frankvg/Pet-Detective/sketch_pet_detective/GIF_cats.h

/*  Pet Detective, by FAQware

These are small GIF images converted into bytes
You will need to change source code and layouts if you elect to change the image sizes
We use this GIF to filearray converter: https://mischianti.org/online-converter-file-to-cpp-gzip-byte-array-3/

Transpanacy MUST be turned off when creating your GIF.  Background should be black.
*/

//File: Cat_Detective_Jacket_141x140.gif, Size: 14034
#define Cat_Detective_Jacket_141x140_gif_len 14034
const uint8_t Cat_Detective_Jacket_141x140_gif[] PROGMEM = {  
0x47, 0x49, 0x46, 0x38, 0x39, 0x61, 0x8D, 0x00, 0x8C, 0x00, 0xF7, 0x00, 0x00, 0xC8, 0xB9, 0xA4, 
0xA9, 0x93, 0x78, 0x88, 0x6B, 0x53, 0xB3, 0x8C, 0x67, 0xC9, 0xB4, 0x99, 0x9A, 0x83, 0x68, 0xB9, 
0xA4, 0x8A, 0x49, 0x2E, 0x18, 0xC3, 0x9C, 0x7B, 0xCA, 0xA4, 0x84, 0xA3, 0x7B, 0x57, 0x93, 0x69, 
0x33, 0x53, 0x3B, 0x28, 0xD6, 0xC2, 0xAA, 0x8C, 0x72, 0x57, 0x26, 0x19, 0x11, 0xB9, 0xA9, 0x95, 
0x59, 0x46, 0x34, 0x97, 0x7C, 0x62, 0x93, 0x6C, 0x4B, 0x8F, 0x5A, 0x2C, 0x6B, 0x51, 0x39, 0xD4, 
0xB2, 0x93, 0xD2, 0xAC, 0x8D, 0xE6, 0xD3, 0xBA, 0x93, 0x72, 0x53, 0x39, 0x2C, 0x22, 0xAA, 0x99, 
0x84, 0xF5, 0xE9, 0xD8, 0xC7, 0xA4, 0x79, 0x9C, 0x7A, 0x5C, 0xE6, 0xC8, 0xA5, 0x7C, 0x61, 0x48, 
0xA8, 0x81, 0x5A, 0xAD, 0x71, 0x34, 0x9A, 0x89, 0x73, 0xB9, 0x92, 0x6A, 0xCE, 0xAA, 0x8B, 0x68, 
0x55, 0x44, 0xD5, 0xB5, 0x8B, 0xEB, 0xDD, 0xCB, 0xC7, 0xA1, 0x82, 0x8D, 0x69, 0x4A, 0x9B, 0x74, 
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
0x2E, 0x34, 0x33, 0x15, 0x18, 0x14, 0x7E, 0x7B, 0x71, 0x26, 0x2A, 0x29, 0x8A, 0x88, 0x88, 0x94, 
0x90, 0x88, 0xDE, 0xDE, 0xDC, 0x67, 0x5F, 0x55, 0x04, 0x02, 0x01, 0xA1, 0xA0, 0x9F, 0x86, 0x89, 
0x7D, 0x65, 0x66, 0x5D, 0xBA, 0xB8, 0xBB, 0x1F, 0x20, 0x1F, 0x6A, 0x6B, 0x66, 0x81, 0x7F, 0x83, 
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
};
