frankvg/Pet-Detective/sketch_pet_detective/GIF_dogs.h

/*  Pet Detective, by FAQware

These are small GIF images converted into bytes
You will need to change source code and layouts if you elect to change the image sizes
We use this GIF to filearray converter: https://mischianti.org/online-converter-file-to-cpp-gzip-byte-array-3/

Transpanacy MUST be turned off when creating your GIF.  Background should be black.
*/

//File: Dog_Detective_Jacket_141x140.gif, Size: 13593
#define Dog_Detective_Jacket_141x140_gif_len 13593
const uint8_t Dog_Detective_Jacket_141x140_gif[] PROGMEM = {  
0x47, 0x49, 0x46, 0x38, 0x39, 0x61, 0x8D, 0x00, 0x8C, 0x00, 0xF7, 0x00, 0x00, 0xD9, 0xA5, 0x65, 
0x74, 0x51, 0x3A, 0x82, 0x5A, 0x3C, 0xA7, 0x69, 0x27, 0x7A, 0x5A, 0x43, 0xA9, 0x73, 0x38, 0xB8, 
0x84, 0x46, 0xD4, 0x97, 0x4A, 0xE8, 0xB8, 0x76, 0x76, 0x46, 0x16, 0xA7, 0x79, 0x47, 0x78, 0x54, 
0x3B, 0x64, 0x39, 0x0F, 0x9A, 0x63, 0x29, 0x84, 0x5C, 0x41, 0xCA, 0x96, 0x57, 0xB7, 0x74, 0x28, 
0x30, 0x2C, 0x2B, 0xD5, 0x9C, 0x54, 0xD7, 0xBA, 0x95, 0xE6, 0xC5, 0x9A, 0xA5, 0x7A, 0x54, 0xE7, 
0xA9, 0x56, 0x42, 0x2B, 0x1B, 0x97, 0x58, 0x18, 0x96, 0x85, 0x73, 0x24, 0x15, 0x0A, 0xF6, 0xCA, 
0x89, 0x7B, 0x62, 0x4A, 0xDC, 0xA3, 0x59, 0x8A, 0x61, 0x38, 0xB6, 0x88, 0x54, 0x57, 0x36, 0x15, 
0xE9, 0xB3, 0x68, 0x5C, 0x44, 0x32, 0x8A, 0x61, 0x43, 0xE7, 0xCA, 0xA3, 0x9C, 0x72, 0x47, 0x5B, 
0x40, 0x2D, 0x28, 0x1A, 0x11, 0xA9, 0x65, 0x1C, 0x7A, 0x51, 0x27, 0x63, 0x45, 0x30, 0xFE, 0xE5, 
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
0xE7, 0xC0, 0x8E, 0xE8, 0xD2, 0xB5, 0xED, 0xD9, 0xBF, 0xE2, 0xDC, 0xD2, 0xF1, 0xCF, 0xA2, 0xE0, 
0xAF, 0x70, 0xA2, 0x9E, 0x95, 0x83, 0x69, 0x64, 0xF1, 0xBE, 0x77, 0xC6, 0x89, 0x43, 0xD8, 0x9E, 
0x58, 0xC1, 0x8E, 0x54, 0xE9, 0xBF, 0x89, 0xC0, 0xBB, 0xB4, 0x9F, 0x91, 0x7D, 0xBF, 0xA1, 0x7D, 
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
};
