frankvg/Pet-Detective/sketch_pet_detective/GIF_general.h

/*  Pet Detective, by FAQware

These are small GIF images converted into bytes
You will need to change source code and layouts if you elect to change the image sizes
We use this GIF to filearray converter: https://mischianti.org/online-converter-file-to-cpp-gzip-byte-array-3/

Transpanacy MUST be turned off when creating your GIF.  Background should be black.
*/

//File: Pet_Detective_Text_155x62.gif, Size: 3084
#define Pet_Detective_Text_155x62_gif_len 3084
const uint8_t Pet_Detective_Text_155x62_gif[] PROGMEM = {
0x47, 0x49, 0x46, 0x38, 0x39, 0x61, 0x9B, 0x00, 0x3E, 0x00, 0xF7, 0x00, 0x00, 0x41, 0x45, 0x8D,
0x5E, 0x64, 0xD1, 0xCC, 0xCD, 0xDD, 0x59, 0x5D, 0xAA, 0x7B, 0x7E, 0xB8, 0x44, 0x49, 0x9C, 0xF3,
0xF3, 0xF4, 0x34, 0x35, 0x42, 0x2B, 0x2C, 0x42, 0x39, 0x3A, 0x42, 0x61, 0x62, 0x7D, 0x64, 0x68,
0xB8, 0x7C, 0x82, 0xE9, 0x94, 0x96, 0xAA, 0x6D, 0x6E, 0x7D, 0x50, 0x54, 0x9C, 0x2B, 0x2D, 0x58,
0x3C, 0x3E, 0x6B, 0x3B, 0x3D, 0x58, 0x3D, 0x41, 0x8D, 0xC0, 0xC0, 0xC5, 0x5D, 0x5E, 0x6B, 0x36,
0x39, 0x6B, 0x49, 0x4D, 0x9C, 0x54, 0x54, 0x58, 0x11, 0x12, 0x26, 0x84, 0x85, 0x8D, 0x65, 0x65,
0x6B, 0xD3, 0xD4, 0xDD, 0x54, 0x54, 0x6B, 0xA5, 0xA6, 0xB8, 0x5C, 0x5D, 0x7D, 0x44, 0x46, 0x6B,
0x35, 0x39, 0x7D, 0x65, 0x66, 0x8D, 0x43, 0x46, 0x7D, 0x99, 0x99, 0x9C, 0x4E, 0x4E, 0x58, 0x76,
0x7B, 0xD1, 0x5E, 0x62, 0xB8, 0x21, 0x21, 0x26, 0x21, 0x23, 0x42, 0x19, 0x1A, 0x26, 0x55, 0x59,
0xB8, 0x25, 0x25, 0x26, 0x72, 0x77, 0xD1, 0x89, 0x8D, 0xD1, 0x6E, 0x72, 0xAA, 0x56, 0x5A, 0x9C,
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
0x84, 0x7D, 0x74, 0x00, 0x25, 0x78, 0x59, 0x25, 0x8C, 0x8D, 0x8F, 0x8D, 0x7F, 0x90, 0x78, 0x92,
0x91, 0x95, 0x67, 0x97, 0x96, 0x99, 0x61, 0x9B, 0x9A, 0x9D, 0x5A, 0x9F, 0x9E, 0xA1, 0x8E, 0xA5,
0x94, 0x93, 0xA3, 0xA2, 0xA7, 0xAA, 0xA6, 0xA9, 0xAC, 0xB0, 0xAF, 0xB2, 0x98, 0xB3, 0x9C, 0xB5,
0xA0, 0xB7, 0xA4, 0xB9, 0xAB, 0xBB, 0xAE, 0xB4, 0xBF, 0xB6, 0xC0, 0xB8, 0xC2, 0xBA, 0xC4, 0xBC,
0xC6, 0xBE, 0x9C, 0x89, 0x72, 0xAD, 0x7F, 0x85, 0x78, 0x88, 0x8D, 0x8B, 0xA9, 0x20, 0x8D, 0x24,
0x20, 0x09, 0x93, 0x09, 0x1C, 0x5A, 0x7D, 0x1C, 0x1D, 0x14, 0xDD, 0x59, 0x14, 0x1D, 0x22, 0x60,
0x67, 0x03, 0x22, 0x05, 0x07, 0x04, 0x61, 0x04, 0x07, 0x05, 0x0F, 0x0E, 0x02, 0x12, 0x04, 0x04,
0x12, 0x02, 0x0E, 0x0F, 0x1E, 0x11, 0x13, 0x10, 0x0D, 0x0D, 0x20, 0x4C, 0x88, 0xE0, 0x21, 0x08,
0x00, 0x3B
};
