frankvg/Pet-Detective/sketch_pet_detective/webpage.h

/*  Pet Detective, by FAQware

Status Web Page

The HTML code is broken up into sections where custom data is inserted when the 
page is built and sent to the requesting browser.

There is a small amount of JavaScript to check with the Pet Detective 'server' every 
6 seconds to see if any transitions have occurred.  If a transition has occured, a 
full page refresh is requested by the JavaScript code. Otherwise, only 26 bytes are 
transfered every 6 seconds. When a full page refresh occurs, it can take several 
seconds for our slow ESP32 processor to generate the page.

Since we don't have a file system, we converted our 32-bit paw-print icon into 
base64 data so we could still display a shortcut icon and a larger inverted
paw print for the backgound (see near the bottom of this page for more details).

11-Mar-2026 (c) FAQware

*/

const String webPageTop = R"HTML_PAGE(
<!doctype html>
<html>
<head>
<link rel="preconnect" href="https://fonts.googleapis.com">
<link rel="preconnect" href="https://fonts.gstatic.com" crossorigin>
<link href="https://fonts.googleapis.com/css2?family=Poetsen+One&display=swap" rel="stylesheet">
<link rel="shortcut icon" href="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
ADAP/4B4H/+Afn//wf//" />
<title>Pet Detective</title>
<script>
window.onload = function() {
  async function refreshCheck() {
   showlog = "n";
   try {
    const queryString = window.location.search;
    if (queryString != null) {
     const urlParams = new URLSearchParams(queryString);
     if (urlParams != null) {
      if (urlParams.get('log') == "y") showlog = "y";
     }
    }
    const url = new URL(window.location.href);
    url.searchParams.set("log", showlog);
    url.searchParams.set("ver", ")HTML_PAGE";

  const String webPageVersion = R"HTML_PAGE(");
    const response = await fetch(url.href);
    if (response.status == 205) { 
     // changed, so force refresh page
     url.searchParams.delete("ver");
     window.location.href = url.href;
    }
   } catch (error) {
     console.error(error.message);
   }
  }
  setInterval(refreshCheck, 6000);	
};
</script>
<!-- <meta http-equiv="refresh" content="30"> -->
<style>
:root {
	--pet-color:#)HTML_PAGE";

const String webPageMiddle = R"HTML_PAGE(;
}
body {
background-color: #000;
}
* {
margin: 0;
padding:0;
box-sizing:border-box;
font-family: Verdana; sans-serif;
text-align: center;
color: #6A67EF;
font-size: 20px;	
}
.module {
position: relative;
}
.module::before {
content: "";
position: absolute;
top: 0; left: 0;
width: 100%; height: 100%;
background-image: url()HTML_PAGE";

const String webPageAfterPaw = R"HTML_PAGE(deg) brightness(80%);
background-color: #000000;
background-repeat: repeat-x;
background-position: 0px 300px;
}
.module-inside {
position: relative;
}
.stat-box {
border: solid var(--pet-color);
border-radius: 10px;
margin: 0 auto;
padding: 0 57px 20px;
font-style: italic;
width: fit-content;
background-color: black;
}
.stat-now {
font-style:normal;
font-weight:bold;
font-size: 54px;
color: var(--pet-color);
padding-bottom: 18px;
}
.stat-at {
font-style:normal;
font-size: 54px;
color: var(--pet-color);
opacity: .8;
padding-bottom: 15px;
}
.stat-grey {
font-style:normal;
font-size: 33px;
color: #BBB;
padding-bottom: 15px;
}
.stat {
transform: translatey(-60%);
width: max-content;
font-style:italic;
padding: 0 12px;
color: #CCC;
font-size: 24px;
background-color: black;	
}
.gradient-text {
font-size: 82px; 
background-image: linear-gradient(to bottom, #FFF, #4641CC); 
-webkit-background-clip: text;
-webkit-text-fill-color: transparent;
display: inline-block; 
font-style:italic;
font-weight: 100;
font-family: "Poetsen One", sans-serif; 
padding-right:30px;
padding-left:30px;
margin-top: 20px;
margin-bottom: 25px;
}  
.log-box {
border: solid #8000FF;
padding-right:30px;
padding-left:30px;
}
table th {
color: #3372FF;
text-align: center;
font-style:normal;
font-size: 20px;
}
table td {
color: #A0A0C0;
font-style:normal;
font-size: 20px;
padding-right:8px;
padding-left:8px;
}
.container {
display: flex;
flex-wrap: nowrap;
}
.left-section {
}
.right-section {
padding-left:20px;
width: 246;
}
</style>
</head>
<body>
<div class="module">
<div class="module-inside">
<h1 class="gradient-text">Pet Detective</h1>
<div class="stat-box">
<div class="stat">Status</div>
<div class="container">
<div class="left-section">)HTML_PAGE";

const String webPageBottom1 = R"HTML_PAGE(
</div>
</div>
</div>
</div>
Copyright 2026 FAQware<br>)HTML_PAGE";

const String webPageBottom2 = R"HTML_PAGE(
</div>
</div>
</body>
</html>)HTML_PAGE";

// This is a single paw png image used in the repeating background line. It 
// also has the hue filter at end. We change the hue rather than having 4 
// different colored paw images.

const String pawImage = 
"data:image/png;base64,iVBORw0KGgoAAAANSUhEUgAAACwAAAA0CAIAAAB+Y02gAAAAGXRFWHRTb2"
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
"CC"
");\n"
"filter: hue-rotate(";
